YummyYae/YummyIMU/源码/user/BSP/bmi260_config_file.h

/*
 * Copyright (c) 2020 Bosch Sensortec GmbH. All rights reserved.
 *
 * Use of this source code is governed by a BSD-style license that can be
 * found in LICENSE.bmi260.
 *
 * @file accelgyro_bmi260_config_tbin.c
 * @date 2020-01-10
 * @version v2.46.1
 * @source ChromiumOS EC third_party/bmi260/accelgyro_bmi260_config_tbin.h
 * @sha256 CF0527E2A34AAF3ACFDF5CA539CFB47C2381693D064B49D1479EBCFAB0CCA377
 *
 */

#ifndef BMI260_CONFIG_FILE_H
#define BMI260_CONFIG_FILE_H

#include <stdint.h>

static const uint8_t gBmi260ConfigFile[] = {
	0xc8, 0x2e, 0x00, 0x2e, 0x80, 0x2e, 0x63, 0xb3, 0xc8, 0x2e, 0x00, 0x2e,
	0x80, 0x2e, 0x15, 0x03, 0x80, 0x2e, 0xbb, 0xb4, 0x80, 0x2e, 0x91, 0x03,
	0xc8, 0x2e, 0x00, 0x2e, 0x80, 0x2e, 0xe7, 0xb3, 0x50, 0x30, 0x21, 0x2e,
	0x59, 0xf5, 0x10, 0x30, 0x21, 0x2e, 0x4a, 0xf1, 0x21, 0x2e, 0x6a, 0xf5,
	0x80, 0x2e, 0xe0, 0x01, 0x0d, 0x0d, 0x01, 0x00, 0x22, 0x00, 0x76, 0x00,
	0x00, 0x10, 0x00, 0x10, 0xc8, 0x00, 0x01, 0x1c, 0x80, 0x2e, 0x00, 0xc1,
	0x80, 0x2e, 0x00, 0xc1, 0x80, 0x2e, 0x00, 0xc1, 0x80, 0x2e, 0x00, 0xc1,
	0x80, 0x2e, 0x00, 0xc1, 0x80, 0x2e, 0x00, 0xc1, 0x80, 0x2e, 0x00, 0xc1,
	0x80, 0x2e, 0x00, 0xc1, 0x80, 0x2e, 0x00, 0xc1, 0x80, 0x2e, 0x00, 0xc1,
	0x80, 0x2e, 0x00, 0xc1, 0x80, 0x2e, 0x00, 0xc1, 0x80, 0x2e, 0x00, 0xc1,
	0x80, 0x2e, 0x00, 0xc1, 0x80, 0x2e, 0x00, 0xc1, 0x80, 0x2e, 0x00, 0xc1,
	0x80, 0x2e, 0x00, 0xc1, 0x80, 0x2e, 0x00, 0xc1, 0x80, 0x2e, 0x00, 0xc1,
	0x80, 0x2e, 0x00, 0xc1, 0x80, 0x2e, 0x00, 0xc1, 0x80, 0x2e, 0x00, 0xc1,
	0x80, 0x2e, 0x00, 0xc1, 0x80, 0x2e, 0x00, 0xc1, 0x80, 0x2e, 0x00, 0xc1,
	0x80, 0x2e, 0x00, 0xc1, 0x80, 0x2e, 0x00, 0xc1, 0x80, 0x2e, 0x00, 0xc1,
	0x80, 0x2e, 0x00, 0xc1, 0x80, 0x2e, 0x00, 0xc1, 0x80, 0x2e, 0x00, 0xc1,
	0x80, 0x2e, 0x00, 0xc1, 0x80, 0x2e, 0x00, 0xc1, 0x80, 0x2e, 0x00, 0xc1,
	0x80, 0x2e, 0x00, 0xc1, 0x80, 0x2e, 0x00, 0xc1, 0x80, 0x2e, 0x00, 0xc1,
	0x80, 0x2e, 0x00, 0xc1, 0x80, 0x2e, 0x00, 0xc1, 0x80, 0x2e, 0x00, 0xc1,
	0x80, 0x2e, 0x00, 0xc1, 0x80, 0x2e, 0x00, 0xc1, 0xfd, 0x2d, 0xe4, 0x78,
	0x00, 0x00, 0x00, 0x00, 0x00, 0x00, 0x00, 0x00, 0x01, 0x00, 0x00, 0x00,
	0x00, 0x00, 0x00, 0x00, 0x00, 0x00, 0x00, 0x00, 0x00, 0x00, 0x00, 0x00,
	0x00, 0x00, 0x00, 0x00, 0x00, 0x00, 0x00, 0x00, 0x0d, 0x0d, 0x00, 0x00,
	0x88, 0x00, 0x05, 0xe0, 0xaa, 0x38, 0x05, 0xe0, 0x90, 0x30, 0x86, 0x00,
	0x30, 0x0a, 0x80, 0x40, 0x10, 0x27, 0xe8, 0x73, 0x04, 0x30, 0x00, 0x02,
	0x00, 0x01, 0x00, 0x30, 0x10, 0x0b, 0x09, 0x08, 0xfa, 0x00, 0x96, 0x00,
	0x4b, 0x09, 0x11, 0x00, 0x11, 0x00, 0x02, 0x00, 0x00, 0x00, 0x22, 0x07,
	0x00, 0x00, 0x00, 0x00, 0x00, 0x00, 0x00, 0x00, 0x00, 0x00, 0x00, 0x00,
	0x00, 0x00, 0x00, 0x00, 0x00, 0x00, 0x00, 0x00, 0x00, 0x00, 0x00, 0x00,
	0x00, 0x00, 0x00, 0x00, 0x00, 0x00, 0x00, 0x00, 0x00, 0x00, 0x00, 0x00,
	0x00, 0x00, 0x00, 0x00, 0x00, 0x00, 0x00, 0x00, 0x00, 0x00, 0x00, 0x00,
	0x00, 0x00, 0x00, 0x00, 0x00, 0x00, 0x00, 0x00, 0x00, 0x00, 0x00, 0x00,
	0x00, 0x00, 0x00, 0x00, 0x00, 0x00, 0x00, 0x00, 0x00, 0x00, 0x00, 0x00,
	0x00, 0x00, 0x00, 0x00, 0x00, 0x00, 0x00, 0x00, 0x00, 0x00, 0x00, 0x00,
	0x00, 0x00, 0x00, 0x00, 0x00, 0x00, 0x00, 0x00, 0x00, 0x00, 0x00, 0x00,
	0x00, 0x00, 0x00, 0x00, 0x00, 0x00, 0x80, 0x00, 0x00, 0x00, 0x00, 0x00,
	0x00, 0x00, 0x01, 0x00, 0x01, 0x00, 0x00, 0x00, 0x00, 0x00, 0x32, 0x01,
	0xe6, 0x78, 0x84, 0x00, 0x9c, 0x6c, 0x07, 0x00, 0x64, 0x75, 0xaa, 0x7e,
	0x5f, 0x05, 0xbe, 0x0a, 0x5f, 0x05, 0x96, 0xe8, 0xef, 0x41, 0x01, 0x00,
	0x0c, 0x00, 0x0c, 0x00, 0x4a, 0x00, 0xa0, 0x00, 0x00, 0x00, 0x0c, 0x00,
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
};

#define BMI260_CONFIG_FILE_SIZE ((uint16_t) sizeof(gBmi260ConfigFile))

#endif
