YummyYae/YummyIMU/源码/user/BSP/bmi220_config_file.h

#ifndef BMI220_CONFIG_FILE_H
#define BMI220_CONFIG_FILE_H

#include <stdint.h>

/*
 * BMI220 config firmware.
 * Source: SlimeVR BMI220 driver, derived from coreboot/chrome-ec
 * third_party/bmi220/accelgyro_bmi220_config_tbin.h (Bosch BSD-3-Clause).
 */
static const uint8_t gBmi220ConfigFile[] = {
    0xc8, 0x2e, 0x00, 0x2e, 0x80, 0x2e, 0xb6, 0xb0, 0xc8, 0x2e, 0x00, 0x2e,
    0x80, 0x2e, 0xee, 0x00, 0x80, 0x2e, 0x6a, 0x01, 0x80, 0x2e, 0xad, 0x01,
    0xc8, 0x2e, 0x00, 0x2e, 0x80, 0x2e, 0x01, 0xb0, 0x50, 0x32, 0x21, 0x2e,
    0x59, 0xf5, 0x10, 0x30, 0x21, 0x2e, 0x6a, 0xf5, 0x80, 0x2e, 0xea, 0x00,
    0x00, 0x00, 0x00, 0x00, 0x3e, 0x21, 0x01, 0x00, 0x22, 0x00, 0x7f, 0x00,
    0x00, 0x0c, 0xff, 0x0f, 0xbc, 0x00, 0x85, 0x33, 0x80, 0x2e, 0x00, 0xc1,
    0x80, 0x2e, 0x00, 0xc1, 0x80, 0x2e, 0x00, 0xc1, 0x80, 0x2e, 0x00, 0xc1,
    0x80, 0x2e, 0x00, 0xc1, 0x80, 0x2e, 0x00, 0xc1, 0x80, 0x2e, 0x00, 0xc1,
    0x80, 0x2e, 0x00, 0xc1, 0x80, 0x2e, 0x00, 0xc1, 0x80, 0x2e, 0x00, 0xc1,
    0x80, 0x2e, 0x00, 0xc1, 0x80, 0x2e, 0x00, 0xc1, 0x80, 0x2e, 0x00, 0xc1,
    0x80, 0x2e, 0x00, 0xc1, 0x80, 0x2e, 0x00, 0xc1, 0x80, 0x2e, 0x00, 0xc1,
    0x80, 0x2e, 0x00, 0xc1, 0x80, 0x2e, 0x00, 0xc1, 0x80, 0x2e, 0x00, 0xc1,
    0x80, 0x2e, 0x00, 0xc1, 0x80, 0x2e, 0x00, 0xc1, 0x80, 0x2e, 0x00, 0xc1,
    0x80, 0x2e, 0x00, 0xc1, 0x80, 0x2e, 0x00, 0xc1, 0x80, 0x2e, 0x00, 0xc1,
    0x80, 0x2e, 0x00, 0xc1, 0x80, 0x2e, 0x00, 0xc1, 0x80, 0x2e, 0x00, 0xc1,
    0x80, 0x2e, 0x00, 0xc1, 0x80, 0x2e, 0x00, 0xc1, 0x80, 0x2e, 0x00, 0xc1,
    0x80, 0x2e, 0x00, 0xc1, 0x80, 0x2e, 0x00, 0xc1, 0x80, 0x2e, 0x00, 0xc1,
    0x80, 0x2e, 0x00, 0xc1, 0x80, 0x2e, 0x00, 0xc1, 0x80, 0x2e, 0x00, 0xc1,
    0x80, 0x2e, 0x00, 0xc1, 0x80, 0x2e, 0x00, 0xc1, 0x80, 0x2e, 0x00, 0xc1,
    0x80, 0x2e, 0x00, 0xc1, 0x80, 0x2e, 0x00, 0xc1, 0x80, 0x2e, 0x00, 0xc1,
    0x80, 0x2e, 0x00, 0xc1, 0x80, 0x2e, 0x00, 0xc1, 0x80, 0x2e, 0x00, 0xc1,
    0x80, 0x2e, 0x00, 0xc1, 0xac, 0xa2, 0x00, 0x00, 0x00, 0x00, 0x00, 0x00,
    0x00, 0x00, 0x00, 0x00, 0x00, 0x00, 0x03, 0x00, 0x32, 0x01, 0xe6, 0x78,
    0x84, 0x00, 0x9c, 0x6c, 0x07, 0x00, 0x64, 0x75, 0xaa, 0x7e, 0x5f, 0x05,
    0xbe, 0x0a, 0x5f, 0x05, 0x96, 0xe8, 0xef, 0x41, 0x01, 0x00, 0x0c, 0x00,
    0x0c, 0x00, 0x4a, 0x00, 0xa0, 0x00, 0x00, 0x00, 0x0c, 0x00, 0xf0, 0x3c,
    0x00, 0x01, 0x00, 0x00, 0x00, 0x00, 0x00, 0x00, 0x00, 0x00, 0x88, 0x00,
    0x00, 0x00, 0x00, 0x00, 0x00, 0x00, 0x00, 0x00, 0x01, 0x00, 0x00, 0x02,
    0x04, 0x00, 0x00, 0x00, 0x00, 0x00, 0x00, 0x00, 0x00, 0x00, 0x00, 0x00,
    0xc1, 0x4a, 0x00, 0x00, 0x6d, 0x57, 0x00, 0x00, 0x77, 0x8e, 0x00, 0x00,
    0xe0, 0xff, 0xff, 0xff, 0xd3, 0xff, 0xff, 0xff, 0xe5, 0xff, 0xff, 0xff,
    0xee, 0xe1, 0xff, 0xff, 0x7c, 0x13, 0x00, 0x00, 0x46, 0xe6, 0xff, 0xff,
    0x1e, 0x00, 0x00, 0x00, 0x00, 0x00, 0x00, 0x00, 0x00, 0x00, 0x00, 0x00,
    0x00, 0x00, 0x00, 0x00, 0x00, 0x00, 0x00, 0x00, 0x00, 0x00, 0x00, 0x00,
    0x00, 0x00, 0x00, 0x00, 0x00, 0x00, 0x00, 0x00, 0x00, 0x00, 0x00, 0x00,
    0x00, 0x00, 0x00, 0x00, 0x00, 0x00, 0x00, 0x00, 0x00, 0x00, 0x00, 0x00,
    0x00, 0x00, 0x00, 0x00, 0x00, 0x00, 0x00, 0x00, 0x00, 0x00, 0x00, 0x00,
    0x00, 0x00, 0x00, 0x00, 0x00, 0x00, 0x00, 0x00, 0x00, 0x00, 0x00, 0x00,
    0x00, 0x00, 0x00, 0x00, 0x00, 0x00, 0x00, 0x00, 0x00, 0x00, 0x00, 0x00,
    0x1a, 0x24, 0x22, 0x00, 0x80, 0x2e, 0x48, 0x02, 0x10, 0x50, 0xf7, 0x7f,
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
};

#define BMI220_CONFIG_FILE_SIZE ((uint16_t) sizeof(gBmi220ConfigFile))

#endif
