YummyYae/YummyIMU/源码/user/BSP/bmi270_config_file.h

#ifndef BMI270_CONFIG_FILE_H
#define BMI270_CONFIG_FILE_H

#include <stdint.h>

static const uint8_t gBmi270ConfigFile[] = {
    0xc8, 0x2e, 0x00, 0x2e, 0x80, 0x2e, 0x3d, 0xb1, 0xc8, 0x2e, 0x00, 0x2e, 0x80, 0x2e, 0x91, 0x03, 0x80, 0x2e, 0xbc,
    0xb0, 0x80, 0x2e, 0xa3, 0x03, 0xc8, 0x2e, 0x00, 0x2e, 0x80, 0x2e, 0x00, 0xb0, 0x50, 0x30, 0x21, 0x2e, 0x59, 0xf5,
    0x10, 0x30, 0x21, 0x2e, 0x6a, 0xf5, 0x80, 0x2e, 0x3b, 0x03, 0x00, 0x00, 0x00, 0x00, 0x08, 0x19, 0x01, 0x00, 0x22,
    0x00, 0x75, 0x00, 0x00, 0x10, 0x00, 0x10, 0xd1, 0x00, 0xb3, 0x43, 0x80, 0x2e, 0x00, 0xc1, 0x80, 0x2e, 0x00, 0xc1,
    0x80, 0x2e, 0x00, 0xc1, 0x80, 0x2e, 0x00, 0xc1, 0x80, 0x2e, 0x00, 0xc1, 0x80, 0x2e, 0x00, 0xc1, 0x80, 0x2e, 0x00,
    0xc1, 0x80, 0x2e, 0x00, 0xc1, 0x80, 0x2e, 0x00, 0xc1, 0x80, 0x2e, 0x00, 0xc1, 0x80, 0x2e, 0x00, 0xc1, 0x80, 0x2e,
    0x00, 0xc1, 0x80, 0x2e, 0x00, 0xc1, 0x80, 0x2e, 0x00, 0xc1, 0x80, 0x2e, 0x00, 0xc1, 0x80, 0x2e, 0x00, 0xc1, 0x80,
    0x2e, 0x00, 0xc1, 0x80, 0x2e, 0x00, 0xc1, 0x80, 0x2e, 0x00, 0xc1, 0x80, 0x2e, 0x00, 0xc1, 0x80, 0x2e, 0x00, 0xc1,
    0x80, 0x2e, 0x00, 0xc1, 0x80, 0x2e, 0x00, 0xc1, 0x80, 0x2e, 0x00, 0xc1, 0x80, 0x2e, 0x00, 0xc1, 0x80, 0x2e, 0x00,
    0xc1, 0x80, 0x2e, 0x00, 0xc1, 0x80, 0x2e, 0x00, 0xc1, 0x80, 0x2e, 0x00, 0xc1, 0x80, 0x2e, 0x00, 0xc1, 0x80, 0x2e,
    0x00, 0xc1, 0x80, 0x2e, 0x00, 0xc1, 0x80, 0x2e, 0x00, 0xc1, 0x80, 0x2e, 0x00, 0xc1, 0x80, 0x2e, 0x00, 0xc1, 0x80,
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
    0x0f, 0x8a, 0x0f, 0xff, 0x03, 0xf0, 0x3f, 0x8b, 0x00, 0x8e, 0x00, 0x90, 0x00, 0xb9, 0x00, 0x2d, 0xf5, 0xca, 0xf5,
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
};

#define BMI270_CONFIG_FILE_SIZE ((uint16_t) sizeof(gBmi270ConfigFile))

#endif
