YummyYae/YummyIMU/源码/user/Task/task_imu.h

#ifndef TASK_IMU_H
#define TASK_IMU_H

#include "runtime_state.h"

#if RUNTIME_FEATURE_INS_ENABLED
#include "inertial_navigation.h"
#endif

#include <stdint.h>

void TaskIMU_Init(RuntimeState_t *state);
uint8_t TaskIMU_HaveFault(const RuntimeState_t *state);
uint8_t TaskIMU_HaveAlarm(const RuntimeState_t *state);
void TaskIMU_EnableInterruptUpdate(uint8_t enable);
void TaskIMU_UpdateFromInterrupt(RuntimeState_t *state);
void TaskIMU_ServiceReport(RuntimeState_t *state);
void TaskIMU_AlignInitialAttitude(void);
#if RUNTIME_FEATURE_INS_ENABLED
uint8_t TaskIMU_RequestNavigationStart(const RuntimeState_t *state);
void TaskIMU_GetNavigationSnapshot(InertialNavigationSnapshot_t *out);
#endif

#endif
