YummyYae/YummyIMU/源码/user/BSP/BMI088reg.h

#ifndef BMI088REG_H
#define BMI088REG_H

#define BMI088_ACC_CHIP_ID 0x00
#define BMI088_ACC_CHIP_ID_VALUE 0x1E

#define BMI088_ACC_STATUS 0x03
#define BMI088_ACCEL_XOUT_L 0x12
#define BMI088_TEMP_M 0x22

#define BMI088_ACC_CONF 0x40
#define BMI088_ACC_CONF_MUST_Set 0x80
#define BMI088_ACC_BWP_SHFITS 0x4
#define BMI088_ACC_NORMAL (0x2 << BMI088_ACC_BWP_SHFITS)
#define BMI088_ACC_ODR_SHFITS 0x0
#define BMI088_ACC_800_HZ (0xB << BMI088_ACC_ODR_SHFITS)

#define BMI088_ACC_RANGE 0x41
#define BMI088_ACC_RANGE_SHFITS 0x0
#define BMI088_ACC_RANGE_6G (0x1 << BMI088_ACC_RANGE_SHFITS)

#define BMI088_INT1_IO_CTRL 0x53
#define BMI088_ACC_INT1_IO_ENABLE_SHFITS 0x3
#define BMI088_ACC_INT1_IO_ENABLE (0x1 << BMI088_ACC_INT1_IO_ENABLE_SHFITS)
#define BMI088_ACC_INT1_GPIO_MODE_SHFITS 0x2
#define BMI088_ACC_INT1_GPIO_PP (0x0 << BMI088_ACC_INT1_GPIO_MODE_SHFITS)
#define BMI088_ACC_INT1_GPIO_LVL_SHFITS 0x1
#define BMI088_ACC_INT1_GPIO_HIGH (0x1 << BMI088_ACC_INT1_GPIO_LVL_SHFITS)

#define BMI088_INT_MAP_DATA 0x58
#define BMI088_ACC_INT1_DRDY_INTERRUPT_SHFITS 0x2
#define BMI088_ACC_INT1_DRDY_INTERRUPT (0x1 << BMI088_ACC_INT1_DRDY_INTERRUPT_SHFITS)

#define BMI088_ACC_PWR_CONF 0x7C
#define BMI088_ACC_PWR_ACTIVE_MODE 0x00
#define BMI088_ACC_PWR_CTRL 0x7D
#define BMI088_ACC_ENABLE_ACC_ON 0x04
#define BMI088_ACC_SOFTRESET 0x7E
#define BMI088_ACC_SOFTRESET_VALUE 0xB6

#define BMI088_GYRO_CHIP_ID 0x00
#define BMI088_GYRO_CHIP_ID_VALUE 0x0F

#define BMI088_GYRO_RANGE 0x0F
#define BMI088_GYRO_RANGE_SHFITS 0x0
#define BMI088_GYRO_2000 (0x0 << BMI088_GYRO_RANGE_SHFITS)

#define BMI088_GYRO_BANDWIDTH 0x10
#define BMI088_GYRO_BANDWIDTH_MUST_Set 0x80
#define BMI088_GYRO_2000_230_HZ 0x01

#define BMI088_GYRO_LPM1 0x11
#define BMI088_GYRO_NORMAL_MODE 0x00
#define BMI088_GYRO_SOFTRESET 0x14
#define BMI088_GYRO_SOFTRESET_VALUE 0xB6
#define BMI088_GYRO_CTRL 0x15
#define BMI088_DRDY_ON 0x80

#define BMI088_GYRO_INT3_INT4_IO_CONF 0x16
#define BMI088_GYRO_INT3_GPIO_MODE_SHFITS 0x1
#define BMI088_GYRO_INT3_GPIO_PP (0x0 << BMI088_GYRO_INT3_GPIO_MODE_SHFITS)
#define BMI088_GYRO_INT3_GPIO_LVL_SHFITS 0x0
#define BMI088_GYRO_INT3_GPIO_HIGH (0x1 << BMI088_GYRO_INT3_GPIO_LVL_SHFITS)

#define BMI088_GYRO_INT3_INT4_IO_MAP 0x18
#define BMI088_GYRO_DRDY_IO_INT3 0x01

#endif
